davidfriar/split45/case/pcbmodels/holes.scad

left_holes = [
  [ 6.82675 , -11.907 , 1.750, "T1" ],
  [ 9.20775 , -30.957 , 1.750, "T1" ],
  [ 13.9707 , -50.007 , 1.750, "T1" ],
  [ 16.9868 , -11.907 , 1.750, "T1" ],
  [ 19.3678 , -30.957 , 1.750, "T1" ],
  [ 21.1137 , -69.057 , 1.750, "T1" ],
  [ 24.1307 , -50.007 , 1.750, "T1" ],
  [ 25.8768 , -11.907 , 1.750, "T1" ],
  [ 30.6388 , -30.957 , 1.750, "T1" ],
  [ 31.2737 , -69.057 , 1.750, "T1" ],
  [ 36.0367 , -11.907 , 1.750, "T1" ],
  [ 40.1638 , -50.007 , 1.750, "T1" ],
  [ 40.7987 , -30.957 , 1.750, "T1" ],
  [ 42.5457 , -69.057 , 1.750, "T1" ],
  [ 44.9267 , -11.907 , 1.750, "T1" ],
  [ 49.6898 , -30.957 , 1.750, "T1" ],
  [ 50.3238 , -50.007 , 1.750, "T1" ],
  [ 52.7057 , -69.057 , 1.750, "T1" ],
  [ 55.0867 , -11.907 , 1.750, "T1" ],
  [ 59.2138 , -50.007 , 1.750, "T1" ],
  [ 59.8487 , -30.957 , 1.750, "T1" ],
  [ 63.9767 , -11.907 , 1.750, "T1" ],
  [ 63.9767 , -69.057 , 1.750, "T1" ],
  [ 68.7387 , -30.957 , 1.750, "T1" ],
  [ 69.3738 , -50.007 , 1.750, "T1" ],
  [ 74.1368 , -11.907 , 1.750, "T1" ],
  [ 74.1368 , -69.057 , 1.750, "T1" ],
  [ 78.2638 , -50.007 , 1.750, "T1" ],
  [ 78.8987 , -30.957 , 1.750, "T1" ],
  [ 83.0267 , -11.907 , 1.750, "T1" ],
  [ 87.7887 , -30.957 , 1.750, "T1" ],
  [ 88.4248 , -50.007 , 1.750, "T1" ],
  [ 93.1868 , -11.907 , 1.750, "T1" ],
  [ 94.9327 , -69.057 , 1.750, "T1" ],
  [ 97.3148 , -50.007 , 1.750, "T1" ],
  [ 97.9488 , -30.957 , 1.750, "T1" ],
  [ 102.077 , -11.907 , 1.750, "T1" ],
  [ 105.093 , -69.057 , 1.750, "T1" ],
  [ 106.839 , -30.957 , 1.750, "T1" ],
  [ 107.474 , -50.007 , 1.750, "T1" ],
  [ 112.237 , -11.907 , 1.750, "T1" ],
  [ 116.364 , -50.007 , 1.750, "T1" ],
  [ 116.999 , -30.957 , 1.750, "T1" ],
  [ 126.524 , -50.007 , 1.750, "T1" ],
  [ 3.17575 , -3.175 , 2.200, "T2" ],
  [ 3.96875 , -76.994 , 2.200, "T2" ],
  [ 115.888 , -3.493 , 2.200, "T2" ],
  [ 119.857 , -76.994 , 2.200, "T2" ],
  [ 130.176 , -41.275 , 2.200, "T2" ],
  [ 88.1068 , -62.072 , 3.048, "T3" ],
  [ 111.92 , -62.072 , 3.048, "T3" ],
  [ 11.9067 , -11.907 , 3.988, "T4" ],
  [ 14.2877 , -30.957 , 3.988, "T4" ],
  [ 19.0508 , -50.007 , 3.988, "T4" ],
  [ 26.1938 , -69.057 , 3.988, "T4" ],
  [ 30.9567 , -11.907 , 3.988, "T4" ],
  [ 35.7188 , -30.957 , 3.988, "T4" ],
  [ 45.2437 , -50.007 , 3.988, "T4" ],
  [ 47.6257 , -69.057 , 3.988, "T4" ],
  [ 50.0067 , -11.907 , 3.988, "T4" ],
  [ 54.7698 , -30.957 , 3.988, "T4" ],
  [ 64.2938 , -50.007 , 3.988, "T4" ],
  [ 69.0567 , -11.907 , 3.988, "T4" ],
  [ 69.0567 , -69.057 , 3.988, "T4" ],
  [ 73.8187 , -30.957 , 3.988, "T4" ],
  [ 83.3438 , -50.007 , 3.988, "T4" ],
  [ 88.1068 , -11.907 , 3.988, "T4" ],
  [ 88.1068 , -77.312 , 3.988, "T4" ],
  [ 92.8688 , -30.957 , 3.988, "T4" ],
  [ 100.013 , -69.057 , 3.988, "T4" ],
  [ 102.394 , -50.007 , 3.988, "T4" ],
  [ 107.157 , -11.907 , 3.988, "T4" ],
  [ 111.92 , -30.957 , 3.988, "T4" ],
  [ 111.92 , -77.312 , 3.988, "T4" ],
  [ 121.444 , -50.007 , 3.988, "T4" ],
];
left_plated_holes = [
  [ 9.74775 , -48.705 , 0.700, "T1" ],
  [ 9.74775 , -51.499 , 0.700, "T1" ],
  [ 7.46175 , -23.337 , 1.092, "T2" ],
  [ 7.46175 , -38.577 , 1.092, "T2" ],
  [ 10.0018 , -23.337 , 1.092, "T2" ],
  [ 10.0018 , -38.577 , 1.092, "T2" ],
  [ 12.5418 , -23.337 , 1.092, "T2" ],
  [ 12.5418 , -38.577 , 1.092, "T2" ],
  [ 15.0817 , -23.337 , 1.092, "T2" ],
  [ 15.0817 , -38.577 , 1.092, "T2" ],
  [ 17.6217 , -23.337 , 1.092, "T2" ],
  [ 17.6217 , -38.577 , 1.092, "T2" ],
  [ 20.1617 , -23.337 , 1.092, "T2" ],
  [ 20.1617 , -38.577 , 1.092, "T2" ],
  [ 22.7017 , -23.337 , 1.092, "T2" ],
  [ 22.7017 , -38.577 , 1.092, "T2" ],
  [ 25.2417 , -23.337 , 1.092, "T2" ],
  [ 25.2417 , -38.577 , 1.092, "T2" ],
  [ 27.7818 , -23.337 , 1.092, "T2" ],
  [ 27.7818 , -38.577 , 1.092, "T2" ],
  [ 30.3218 , -23.337 , 1.092, "T2" ],
  [ 30.3218 , -38.577 , 1.092, "T2" ],
  [ 32.8618 , -23.337 , 1.092, "T2" ],
  [ 32.8618 , -38.577 , 1.092, "T2" ],
  [ 35.4017 , -23.337 , 1.092, "T2" ],
  [ 35.4017 , -38.577 , 1.092, "T2" ],
  [ 8.09675 , -9.367 , 1.470, "T3" ],
  [ 10.4778 , -28.417 , 1.470, "T3" ],
  [ 14.4467 , -6.827 , 1.470, "T3" ],
  [ 15.2407 , -47.467 , 1.470, "T3" ],
  [ 16.8278 , -25.877 , 1.470, "T3" ],
  [ 21.5907 , -44.927 , 1.470, "T3" ],
  [ 22.3837 , -66.517 , 1.470, "T3" ],
  [ 27.1467 , -9.367 , 1.470, "T3" ],
  [ 28.7338 , -63.977 , 1.470, "T3" ],
  [ 31.9098 , -28.417 , 1.470, "T3" ],
  [ 33.4967 , -6.827 , 1.470, "T3" ],
  [ 38.2587 , -25.877 , 1.470, "T3" ],
  [ 41.4337 , -47.467 , 1.470, "T3" ],
  [ 43.8158 , -66.517 , 1.470, "T3" ],
  [ 46.1968 , -9.367 , 1.470, "T3" ],
  [ 47.7848 , -44.927 , 1.470, "T3" ],
  [ 50.1658 , -63.977 , 1.470, "T3" ],
  [ 50.9587 , -28.417 , 1.470, "T3" ],
  [ 52.5468 , -6.827 , 1.470, "T3" ],
  [ 57.3088 , -25.877 , 1.470, "T3" ],
  [ 60.4848 , -47.467 , 1.470, "T3" ],
  [ 65.2468 , -9.367 , 1.470, "T3" ],
  [ 65.2468 , -66.517 , 1.470, "T3" ],
  [ 66.8337 , -44.927 , 1.470, "T3" ],
  [ 70.0088 , -28.417 , 1.470, "T3" ],
  [ 71.5968 , -6.827 , 1.470, "T3" ],
  [ 71.5968 , -63.977 , 1.470, "T3" ],
  [ 76.3588 , -25.877 , 1.470, "T3" ],
  [ 79.5348 , -47.467 , 1.470, "T3" ],
  [ 84.2968 , -9.367 , 1.470, "T3" ],
  [ 85.8838 , -44.927 , 1.470, "T3" ],
  [ 89.0588 , -28.417 , 1.470, "T3" ],
  [ 90.6467 , -6.827 , 1.470, "T3" ],
  [ 95.4098 , -25.877 , 1.470, "T3" ],
  [ 96.2027 , -66.517 , 1.470, "T3" ],
  [ 98.5837 , -47.467 , 1.470, "T3" ],
  [ 102.553 , -63.977 , 1.470, "T3" ],
  [ 103.347 , -9.367 , 1.470, "T3" ],
  [ 104.934 , -44.927 , 1.470, "T3" ],
  [ 108.109 , -28.417 , 1.470, "T3" ],
  [ 109.697 , -6.827 , 1.470, "T3" ],
  [ 114.459 , -25.877 , 1.470, "T3" ],
  [ 117.634 , -47.467 , 1.470, "T3" ],
  [ 123.985 , -44.927 , 1.470, "T3" ],
];
right_holes = [
  [ 6.82675 , -11.907 , 1.750, "T1" ],
  [ 11.5897 , -30.957 , 1.750, "T1" ],
  [ 16.9868 , -11.907 , 1.750, "T1" ],
  [ 21.1137 , -50.007 , 1.750, "T1" ],
  [ 21.7488 , -30.957 , 1.750, "T1" ],
  [ 25.8768 , -11.907 , 1.750, "T1" ],
  [ 28.2578 , -69.057 , 1.750, "T1" ],
  [ 30.6388 , -30.957 , 1.750, "T1" ],
  [ 31.2737 , -50.007 , 1.750, "T1" ],
  [ 36.0367 , -11.907 , 1.750, "T1" ],
  [ 38.4177 , -69.057 , 1.750, "T1" ],
  [ 40.1638 , -50.007 , 1.750, "T1" ],
  [ 40.7987 , -30.957 , 1.750, "T1" ],
  [ 44.9267 , -11.907 , 1.750, "T1" ],
  [ 49.6898 , -30.957 , 1.750, "T1" ],
  [ 50.3238 , -50.007 , 1.750, "T1" ],
  [ 55.0867 , -11.907 , 1.750, "T1" ],
  [ 59.2138 , -50.007 , 1.750, "T1" ],
  [ 59.8487 , -30.957 , 1.750, "T1" ],
  [ 63.9767 , -11.907 , 1.750, "T1" ],
  [ 63.9767 , -69.057 , 1.750, "T1" ],
  [ 68.7387 , -30.957 , 1.750, "T1" ],
  [ 69.3738 , -50.007 , 1.750, "T1" ],
  [ 74.1368 , -11.907 , 1.750, "T1" ],
  [ 74.1368 , -69.057 , 1.750, "T1" ],
  [ 78.2638 , -50.007 , 1.750, "T1" ],
  [ 78.8987 , -30.957 , 1.750, "T1" ],
  [ 83.0267 , -11.907 , 1.750, "T1" ],
  [ 85.4077 , -69.057 , 1.750, "T1" ],
  [ 87.7887 , -30.957 , 1.750, "T1" ],
  [ 88.4248 , -50.007 , 1.750, "T1" ],
  [ 93.1868 , -11.907 , 1.750, "T1" ],
  [ 95.5678 , -69.057 , 1.750, "T1" ],
  [ 97.3148 , -50.007 , 1.750, "T1" ],
  [ 97.9488 , -30.957 , 1.750, "T1" ],
  [ 102.077 , -11.907 , 1.750, "T1" ],
  [ 106.839 , -69.057 , 1.750, "T1" ],
  [ 107.474 , -50.007 , 1.750, "T1" ],
  [ 112.237 , -11.907 , 1.750, "T1" ],
  [ 113.983 , -30.957 , 1.750, "T1" ],
  [ 116.999 , -69.057 , 1.750, "T1" ],
  [ 118.746 , -50.007 , 1.750, "T1" ],
  [ 121.127 , -11.907 , 1.750, "T1" ],
  [ 124.143 , -30.957 , 1.750, "T1" ],
  [ 128.906 , -50.007 , 1.750, "T1" ],
  [ 131.287 , -11.907 , 1.750, "T1" ],
  [ 3.17575 , -3.493 , 2.200, "T2" ],
  [ 8.73175 , -76.994 , 2.200, "T2" ],
  [ 17.4627 , -41.275 , 2.200, "T2" ],
  [ 134.144 , -76.994 , 2.200, "T2" ],
  [ 134.938 , -3.493 , 2.200, "T2" ],
  [ 21.4318 , -62.072 , 3.048, "T3" ],
  [ 45.2437 , -62.072 , 3.048, "T3" ],
  [ 11.9067 , -11.907 , 3.988, "T4" ],
  [ 16.6688 , -30.957 , 3.988, "T4" ],
  [ 21.4318 , -77.312 , 3.988, "T4" ],
  [ 26.1938 , -50.007 , 3.988, "T4" ],
  [ 30.9567 , -11.907 , 3.988, "T4" ],
  [ 33.3377 , -69.057 , 3.988, "T4" ],
  [ 35.7188 , -30.957 , 3.988, "T4" ],
  [ 45.2437 , -50.007 , 3.988, "T4" ],
  [ 45.2437 , -77.312 , 3.988, "T4" ],
  [ 50.0067 , -11.907 , 3.988, "T4" ],
  [ 54.7698 , -30.957 , 3.988, "T4" ],
  [ 64.2938 , -50.007 , 3.988, "T4" ],
  [ 69.0567 , -11.907 , 3.988, "T4" ],
  [ 69.0567 , -69.057 , 3.988, "T4" ],
  [ 73.8187 , -30.957 , 3.988, "T4" ],
  [ 83.3438 , -50.007 , 3.988, "T4" ],
  [ 88.1068 , -11.907 , 3.988, "T4" ],
  [ 90.4878 , -69.057 , 3.988, "T4" ],
  [ 92.8688 , -30.957 , 3.988, "T4" ],
  [ 102.394 , -50.007 , 3.988, "T4" ],
  [ 107.157 , -11.907 , 3.988, "T4" ],
  [ 111.92 , -69.057 , 3.988, "T4" ],
  [ 119.063 , -30.957 , 3.988, "T4" ],
  [ 123.826 , -50.007 , 3.988, "T4" ],
  [ 126.207 , -11.907 , 3.988, "T4" ],
];
right_plated_holes = [
  [ 127.921 , -29.528 , 0.700, "T1" ],
  [ 127.921 , -32.322 , 0.700, "T1" ],
  [ 102.712 , -23.337 , 1.092, "T2" ],
  [ 102.712 , -38.577 , 1.092, "T2" ],
  [ 105.252 , -23.337 , 1.092, "T2" ],
  [ 105.252 , -38.577 , 1.092, "T2" ],
  [ 107.792 , -23.337 , 1.092, "T2" ],
  [ 107.792 , -38.577 , 1.092, "T2" ],
  [ 110.332 , -23.337 , 1.092, "T2" ],
  [ 110.332 , -38.577 , 1.092, "T2" ],
  [ 112.872 , -23.337 , 1.092, "T2" ],
  [ 112.872 , -38.577 , 1.092, "T2" ],
  [ 115.412 , -23.337 , 1.092, "T2" ],
  [ 115.412 , -38.577 , 1.092, "T2" ],
  [ 117.952 , -23.337 , 1.092, "T2" ],
  [ 117.952 , -38.577 , 1.092, "T2" ],
  [ 120.492 , -23.337 , 1.092, "T2" ],
  [ 120.492 , -38.577 , 1.092, "T2" ],
  [ 123.032 , -23.337 , 1.092, "T2" ],
  [ 123.032 , -38.577 , 1.092, "T2" ],
  [ 125.572 , -23.337 , 1.092, "T2" ],
  [ 125.572 , -38.577 , 1.092, "T2" ],
  [ 128.112 , -23.337 , 1.092, "T2" ],
  [ 128.112 , -38.577 , 1.092, "T2" ],
  [ 130.652 , -23.337 , 1.092, "T2" ],
  [ 130.652 , -38.577 , 1.092, "T2" ],
  [ 8.09675 , -9.367 , 1.470, "T3" ],
  [ 12.8588 , -28.417 , 1.470, "T3" ],
  [ 14.4467 , -6.827 , 1.470, "T3" ],
  [ 19.2088 , -25.877 , 1.470, "T3" ],
  [ 22.3837 , -47.467 , 1.470, "T3" ],
  [ 27.1467 , -9.367 , 1.470, "T3" ],
  [ 28.7338 , -44.927 , 1.470, "T3" ],
  [ 29.5277 , -66.517 , 1.470, "T3" ],
  [ 31.9098 , -28.417 , 1.470, "T3" ],
  [ 33.4967 , -6.827 , 1.470, "T3" ],
  [ 35.8777 , -63.977 , 1.470, "T3" ],
  [ 38.2587 , -25.877 , 1.470, "T3" ],
  [ 41.4337 , -47.467 , 1.470, "T3" ],
  [ 46.1968 , -9.367 , 1.470, "T3" ],
  [ 47.7848 , -44.927 , 1.470, "T3" ],
  [ 50.9587 , -28.417 , 1.470, "T3" ],
  [ 52.5468 , -6.827 , 1.470, "T3" ],
  [ 57.3088 , -25.877 , 1.470, "T3" ],
  [ 60.4848 , -47.467 , 1.470, "T3" ],
  [ 65.2468 , -9.367 , 1.470, "T3" ],
  [ 65.2468 , -66.517 , 1.470, "T3" ],
  [ 66.8337 , -44.927 , 1.470, "T3" ],
  [ 70.0088 , -28.417 , 1.470, "T3" ],
  [ 71.5968 , -6.827 , 1.470, "T3" ],
  [ 71.5968 , -63.977 , 1.470, "T3" ],
  [ 76.3588 , -25.877 , 1.470, "T3" ],
  [ 79.5348 , -47.467 , 1.470, "T3" ],
  [ 84.2968 , -9.367 , 1.470, "T3" ],
  [ 85.8838 , -44.927 , 1.470, "T3" ],
  [ 86.6778 , -66.517 , 1.470, "T3" ],
  [ 89.0588 , -28.417 , 1.470, "T3" ],
  [ 90.6467 , -6.827 , 1.470, "T3" ],
  [ 93.0277 , -63.977 , 1.470, "T3" ],
  [ 95.4098 , -25.877 , 1.470, "T3" ],
  [ 98.5837 , -47.467 , 1.470, "T3" ],
  [ 103.347 , -9.367 , 1.470, "T3" ],
  [ 104.934 , -44.927 , 1.470, "T3" ],
  [ 108.109 , -66.517 , 1.470, "T3" ],
  [ 109.697 , -6.827 , 1.470, "T3" ],
  [ 114.459 , -63.977 , 1.470, "T3" ],
  [ 115.253 , -28.417 , 1.470, "T3" ],
  [ 120.016 , -47.467 , 1.470, "T3" ],
  [ 121.603 , -25.877 , 1.470, "T3" ],
  [ 122.397 , -9.367 , 1.470, "T3" ],
  [ 126.366 , -44.927 , 1.470, "T3" ],
  [ 128.747 , -6.827 , 1.470, "T3" ],
];
left_base_holes = [
  [ 7.14375 , -3.175 , 2.200, "T1" ],
  [ 7.93775 , -76.994 , 2.200, "T1" ],
  [ 111.92 , -3.493 , 2.200, "T1" ],
  [ 115.888 , -76.994 , 2.200, "T1" ],
  [ 130.176 , -50.007 , 2.200, "T1" ],
];
left_plated_base_holes = [
];
right_base_holes = [
  [ 7.14375 , -3.175 , 2.200, "T1" ],
  [ 12.7007 , -76.994 , 2.200, "T1" ],
  [ 17.4627 , -50.007 , 2.200, "T1" ],
  [ 130.176 , -76.994 , 2.200, "T1" ],
  [ 130.969 , -3.175 , 2.200, "T1" ],
];
right_plated_base_holes = [
];
